trueDKstudent/HDSP_watch/project/HDSP_watch/HDSP_watch/glcdfont.c

#include <avr/io.h>
#include <avr/pgmspace.h>

// Standard ASCII 5x7 font

static const unsigned char font[] PROGMEM = {
	0x00, 0x00, 0x00, 0x00, 0x00,// (space)
	0x00, 0x00, 0x5F, 0x00, 0x00,// !
	0x00, 0x07, 0x00, 0x07, 0x00,// "
	0x14, 0x7F, 0x14, 0x7F, 0x14,// #
	0x24, 0x2A, 0x7F, 0x2A, 0x12,// $
	0x23, 0x13, 0x08, 0x64, 0x62,// %
	0x36, 0x49, 0x55, 0x22, 0x50,// &
	0x00, 0x05, 0x03, 0x00, 0x00,// '
	0x00, 0x1C, 0x22, 0x41, 0x00,// (
	0x00, 0x41, 0x22, 0x1C, 0x00,// )
	0x08, 0x2A, 0x1C, 0x2A, 0x08,// *
	0x08, 0x08, 0x3E, 0x08, 0x08,// +
	0x00, 0x50, 0x30, 0x00, 0x00,// ,
	0x08, 0x08, 0x08, 0x08, 0x08,// -
	0x00, 0x60, 0x60, 0x00, 0x00,// .
	0x20, 0x10, 0x08, 0x04, 0x02,// /
	0x3E, 0x51, 0x49, 0x45, 0x3E,// 0
	0x00, 0x42, 0x7F, 0x40, 0x00,// 1
	0x42, 0x61, 0x51, 0x49, 0x46,// 2
	0x21, 0x41, 0x45, 0x4B, 0x31,// 3
	0x18, 0x14, 0x12, 0x7F, 0x10,// 4
	0x27, 0x45, 0x45, 0x45, 0x39,// 5
	0x3C, 0x4A, 0x49, 0x49, 0x30,// 6
	0x01, 0x71, 0x09, 0x05, 0x03,// 7
	0x36, 0x49, 0x49, 0x49, 0x36,// 8
	0x06, 0x49, 0x49, 0x29, 0x1E,// 9
	0x00, 0x36, 0x36, 0x00, 0x00,// :
	0x00, 0x56, 0x36, 0x00, 0x00,// ;
	0x00, 0x08, 0x14, 0x22, 0x41,// <
	0x14, 0x14, 0x14, 0x14, 0x14,// =
	0x41, 0x22, 0x14, 0x08, 0x00,// >
	0x02, 0x01, 0x51, 0x09, 0x06,// ?
	0x32, 0x49, 0x79, 0x41, 0x3E,// @
	0x7E, 0x11, 0x11, 0x11, 0x7E,// A
	0x7F, 0x49, 0x49, 0x49, 0x36,// B
	0x3E, 0x41, 0x41, 0x41, 0x22,// C
	0x7F, 0x41, 0x41, 0x22, 0x1C,// D
	0x7F, 0x49, 0x49, 0x49, 0x41,// E
	0x7F, 0x09, 0x09, 0x01, 0x01,// F
	0x3E, 0x41, 0x41, 0x51, 0x32,// G
	0x7F, 0x08, 0x08, 0x08, 0x7F,// H
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
};

static const char Mon[] PROGMEM = "Monday, ";
static const char Tue[] PROGMEM = "Tuesday, ";
static const char Wed[] PROGMEM = "Wednesday, ";
static const char Thu[] PROGMEM = "Thursday, ";
static const char Fri[] PROGMEM = "Friday, ";
static const char Sat[] PROGMEM = "Saturday, ";
static const char Sun[] PROGMEM = "Sunday, ";

static const char *const days_table[] PROGMEM = {Mon, Tue, Wed, Thu, Fri, Sat, Sun};

static const char Jan[] PROGMEM = "January 20";
static const char Feb[] PROGMEM = "February 20";
static const char Mar[] PROGMEM = "March 20";
static const char Apr[] PROGMEM = "April 20";
static const char May[] PROGMEM = "May 20";
static const char Jun[] PROGMEM = "June 20";
static const char Jul[] PROGMEM = "July 20";
static const char Aug[] PROGMEM = "August 20";
static const char Sep[] PROGMEM = "September 20";
static const char Oct[] PROGMEM = "October 20";
static const char Nov[] PROGMEM = "November 20";
static const char Dec[] PROGMEM = "December 20";

static const char *const monthes_table[] PROGMEM = {
	Jan, Feb, Mar, Apr, May, Jun, Jul, Aug, Sep, Oct, Nov, Dec
};

static const char hor_set[] PROGMEM = "Hour:   ";
static const char min_set[] PROGMEM = "Min:    ";
static const char sec_set[] PROGMEM = "Sec:    ";

static const char day_set[] PROGMEM = "Day:    ";
static const char mon_set[] PROGMEM = "Mon:    ";
static const char date_set[] PROGMEM = "Date:   ";
static const char year_set[] PROGMEM = "Year:   ";

static const char *const set_table[] PROGMEM = {
	year_set, date_set, mon_set, day_set, sec_set, min_set, hor_set
};
